airqo-platform/AirQo-hardware/docs/deployment/images/analytics-dashboard.png

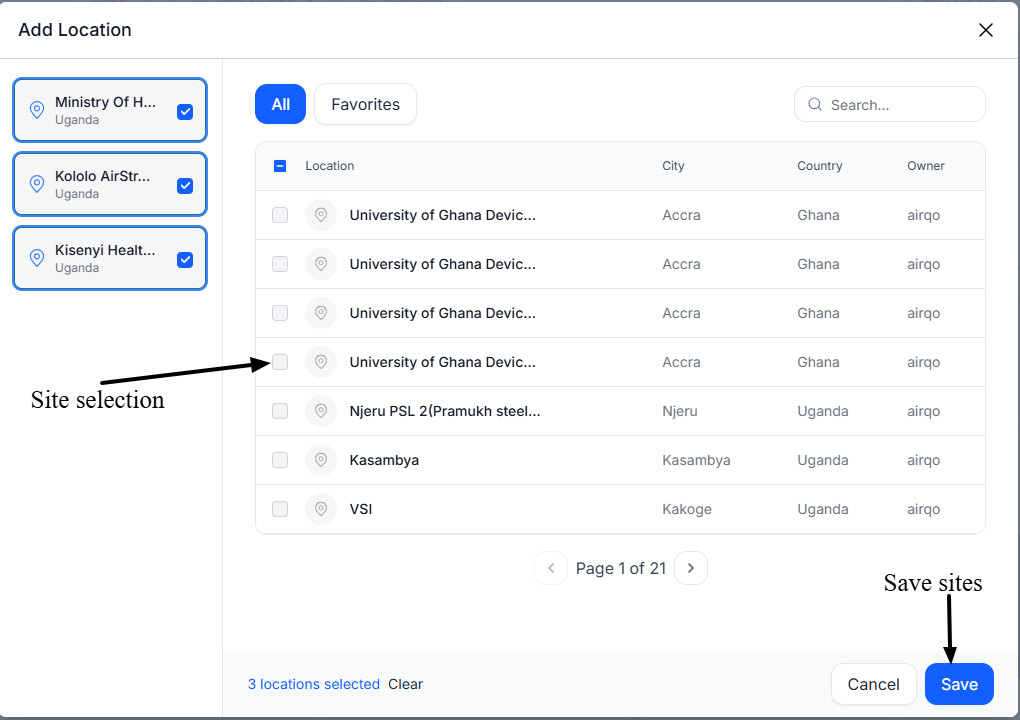
docs/deployment/images/analytics-dashboard.png
