airqo-platform/AirQo-hardware/docs/device/images/monitor-green.png

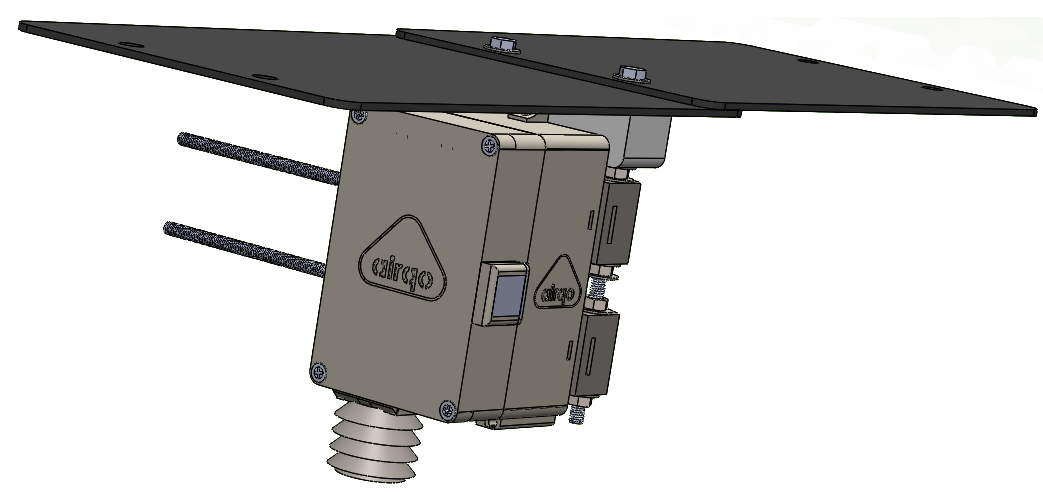
docs/device/images/monitor-green.png
