airqo-platform/AirQo-hardware/docs/maintenance/images/maintenance-doc.png

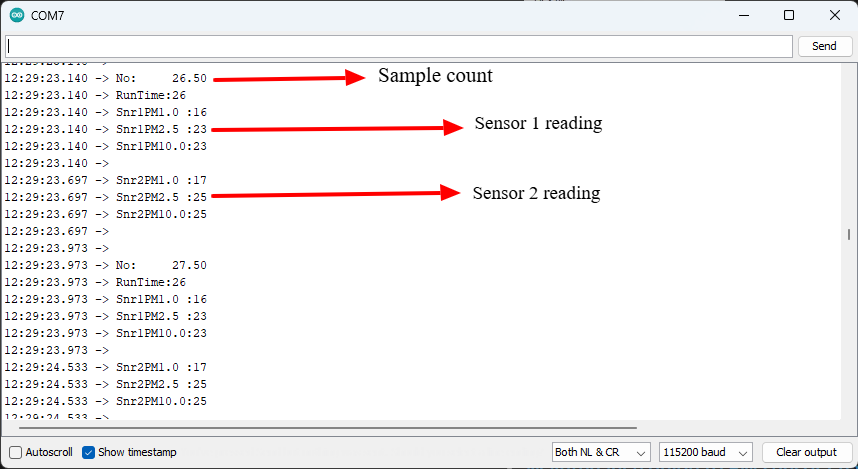
docs/maintenance/images/maintenance-doc.png
